TimothyMarchant/PIC_Watch/PIC_Watch_Source/MCP7940_Files/I2C_Drivers_PIC16F15225.h

#ifndef I2C_Drivers_h
#define I2C_Drivers_h
_Bool I2C_Wait(void);
void I2C_Start(void);
void I2C_Restart(void);
void I2C_Stop(void);
unsigned char I2C_Write(unsigned char data);
#endif
#ifndef I2C_Read_h
#define I2C_Read_h
unsigned char I2C_Read(void);
void ACK(void);
void NACK(void);
#endif
#ifndef I2C_Recovery_h
void ForceReset(void);
#endif
